matias-levy/peaks/firmware/peaks2/resources.cc

// Copyright 2013 Olivier Gillet.
//
// Author: Olivier Gillet (ol.gillet@gmail.com)
//
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
// See http://creativecommons.org/licenses/MIT/ for more information.
//
// -----------------------------------------------------------------------------
//
// Resources definitions.
//
// Automatically generated with:
// make resources


#include "peaks2/resources.h"

namespace peaks {

static const char str_dummy[] = "dummy";


const char* string_table[] = {
  str_dummy,
};

const uint16_t lut_delay_times[] = {
       5,      7,      8,     10,
      12,     14,     16,     18,
      21,     24,     27,     31,
      34,     39,     43,     48,
      53,     59,     65,     71,
      78,     85,     93,    101,
     109,    118,    128,    138,
     149,    160,    172,    185,
     198,    212,    226,    241,
     257,    273,    290,    308,
     327,    347,    367,    388,
     410,    433,    456,    481,
     506,    533,    560,    588,
     617,    648,    679,    711,
     745,    779,    815,    851,
     889,    928,    968,   1009,
    1052,   1096,   1141,   1187,
    1235,   1284,   1334,   1386,
    1439,   1493,   1549,   1607,
    1666,   1726,   1788,   1851,
    1916,   1982,   2050,   2120,
    2192,   2265,   2339,   2416,
    2494,   2574,   2655,   2739,
    2824,   2911,   3000,   3091,
    3184,   3278,   3375,   3474,
    3574,   3677,   3782,   3888,
    3997,   4108,   4221,   4337,
    4454,   4574,   4696,   4820,
    4946,   5075,   5206,   5340,
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
  -32720, -32719, -32718, -32717,
  -32716, -32715, -32714, -32713,
  -32712, -32711, -32710, -32709,
  -32707, -32706, -32705, -32704,
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
};


const int16_t* waveform_table[] = {
  wav_sine,
  wav_fold_power,
  wav_fold_sine,
  wav_overdrive,
};


}  // namespace peaks
